mariusmym/ATtiny-Focus-Timer/images/IMG_0472.JPEG

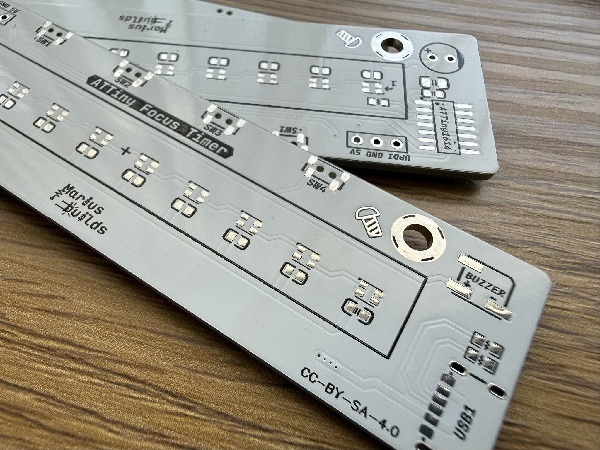
images/IMG_0472.JPEG
