mariusmym/ATtiny-Focus-Timer/images/IMG_0651.jpg

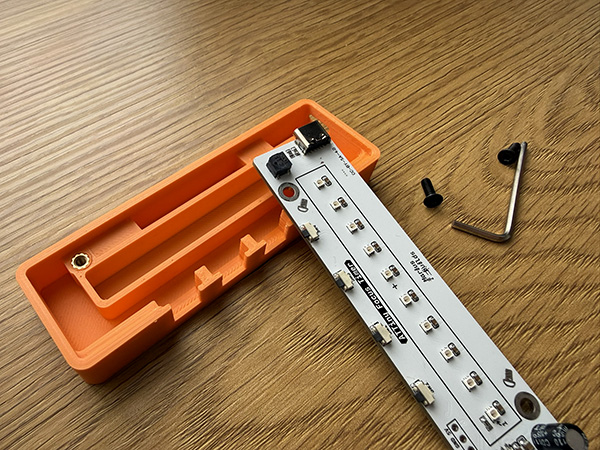
images/IMG_0651.jpg
