mariusmym/ATtiny-Focus-Timer/images/IMG_0653.jpg

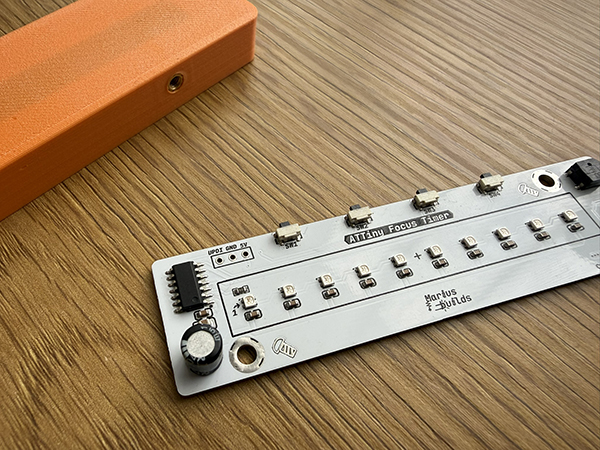
images/IMG_0653.jpg
