mariusmym/ATtiny-Focus-Timer/images/IMG_0657.jpg

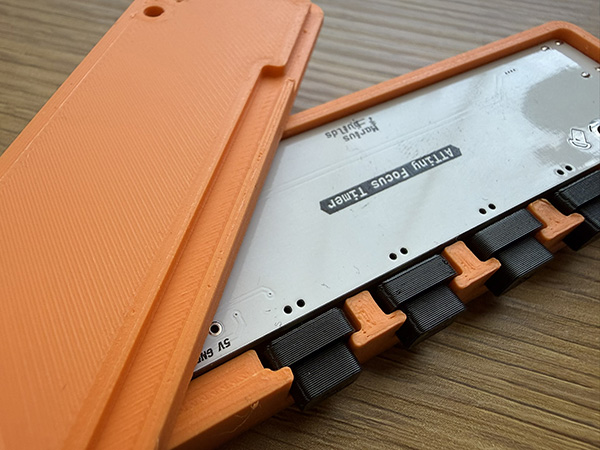
images/IMG_0657.jpg
