mariusmym/ATtiny-Focus-Timer/images/IMG_0670.jpg

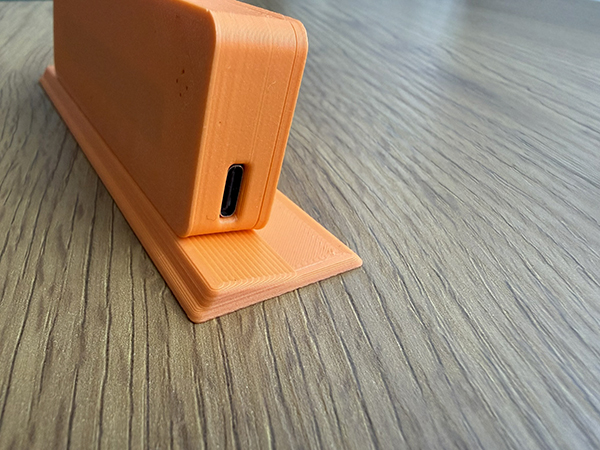
images/IMG_0670.jpg
