mariusmym/ATtiny-Focus-Timer/images/IMG_0679.jpg

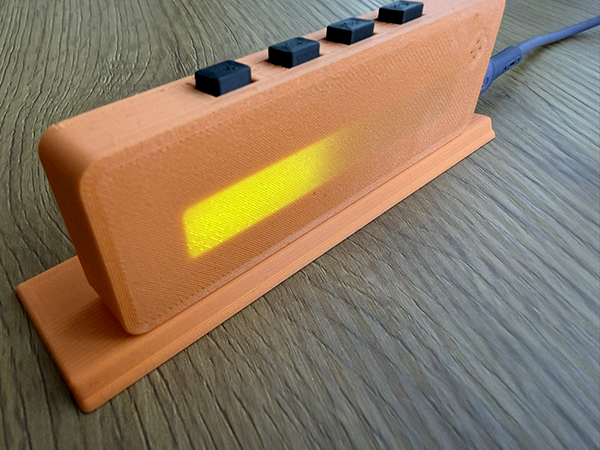
images/IMG_0679.jpg
