mariusmym/ATtiny-Focus-Timer/images/IMG_0681.jpg

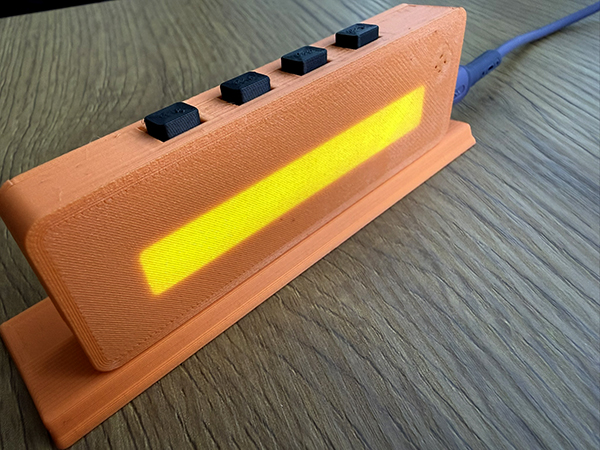
images/IMG_0681.jpg
