mariusmym/ATtiny-Focus-Timer/images/IMG_0701.jpg

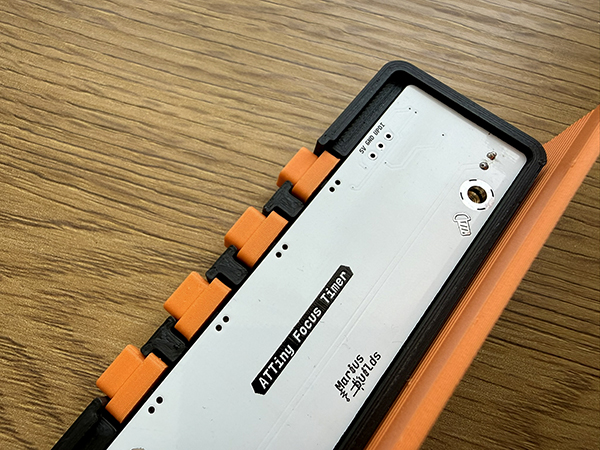
images/IMG_0701.jpg
