mariusmym/ATtiny-Focus-Timer/images/IMG_0703.jpg

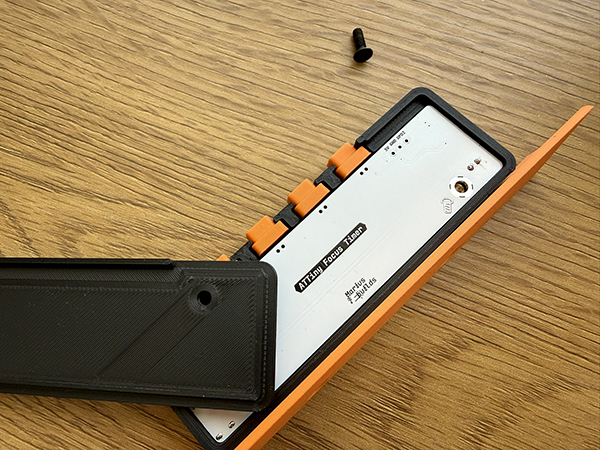
images/IMG_0703.jpg
