mariusmym/ATtiny-Focus-Timer/images/IMG_0705.jpg

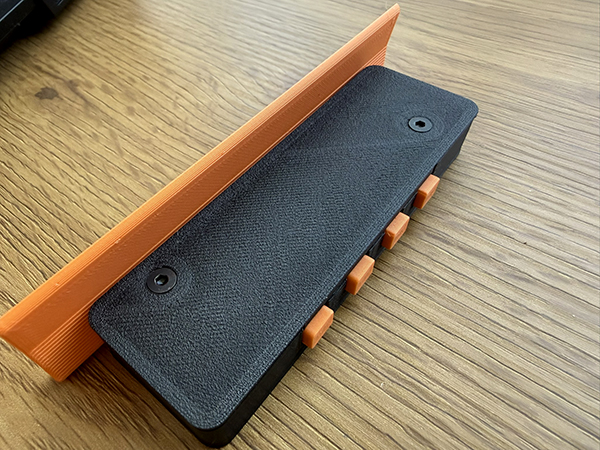
images/IMG_0705.jpg
