mariusmym/ATtiny-Focus-Timer/images/IMG_0709.JPEG

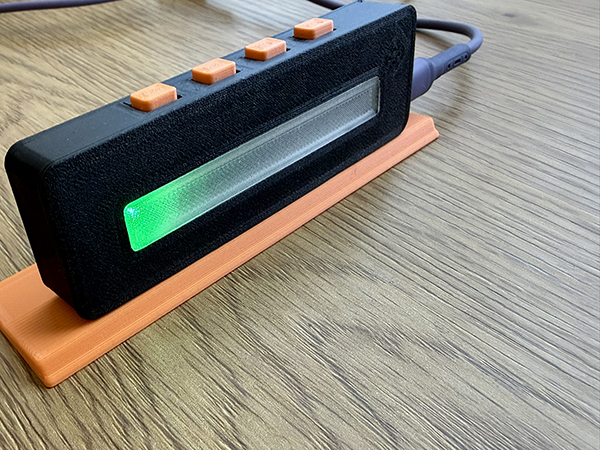
images/IMG_0709.JPEG
