mariusmym/ATtiny-Focus-Timer/images/IMG_0828.JPEG

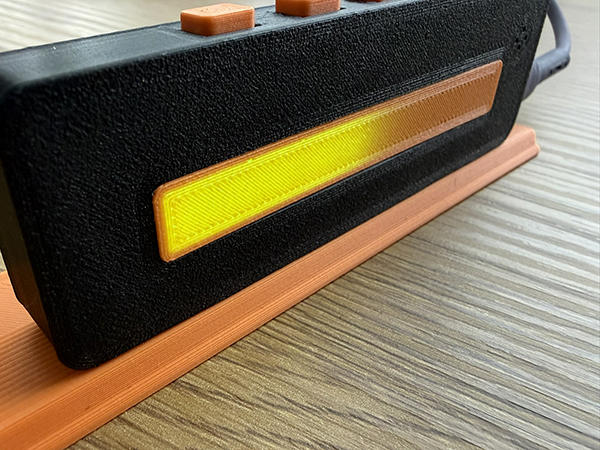
images/IMG_0828.JPEG
