mariusmym/ATtiny-Focus-Timer/images/IMG_0829.JPEG

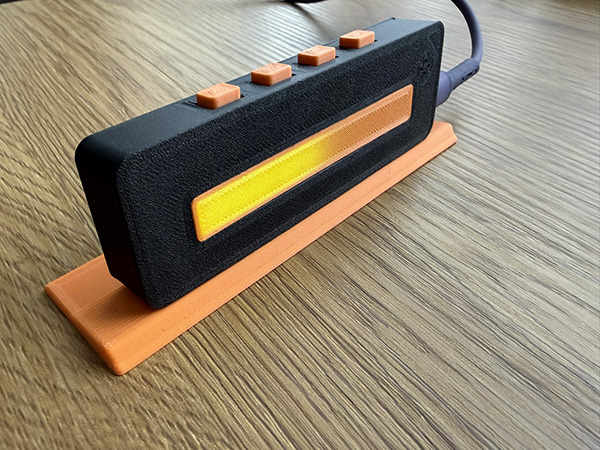
images/IMG_0829.JPEG
