mariusmym/ATtiny-Focus-Timer/images/IMG_0831.jpg

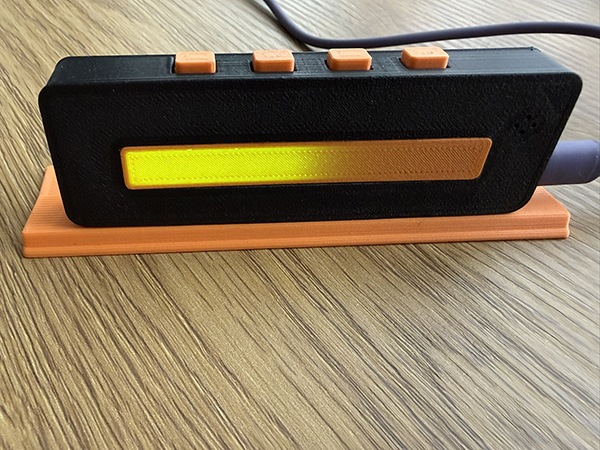
images/IMG_0831.jpg
